enjrolas/L3D-Hardware/16x16x16 cube/3D model/corner.SLDPRT

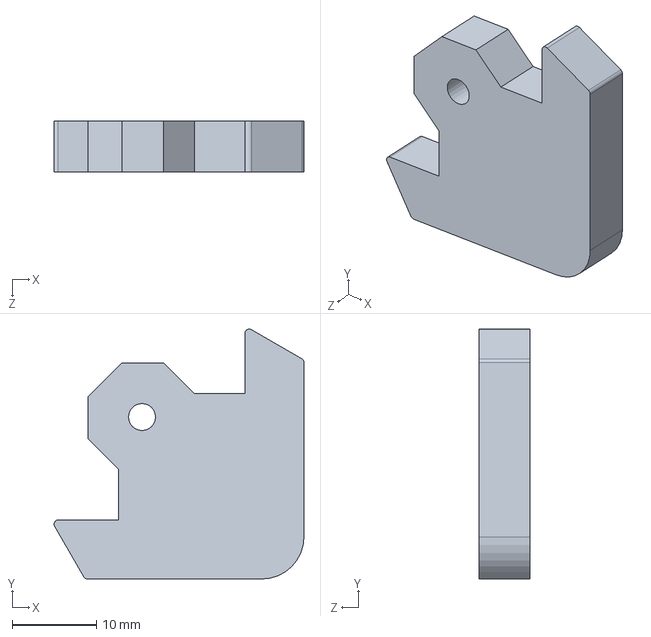
[picture p17: CAD file, 2017-03-31]
16x16x16 cube/3D model/corner.SLDPRT
29.6 x 29.6 x 6.00 mm
