enjrolas/L3D-Hardware/16x16x16 cube/3D model/pcb_strick.SLDPRT

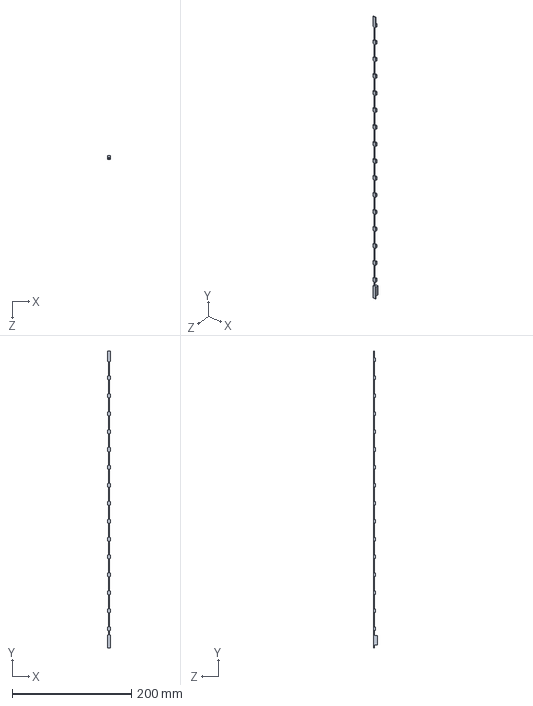
[picture p18: CAD file, 2017-03-31]
16x16x16 cube/3D model/pcb_strick.SLDPRT
5.58 x 497.5 x 6.00 mm
