enjrolas/L3D-Hardware/16x16x16 cube/3D model/white connector.SLDPRT

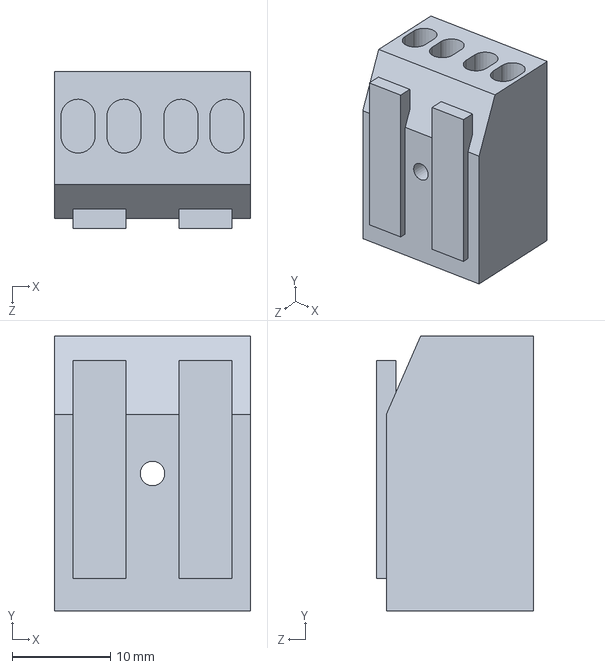
[picture p19: CAD file, 2017-03-31]
16x16x16 cube/3D model/white connector.SLDPRT
20.0 x 28.0 x 16.0 mm
