enjrolas/L3D-Hardware/16x16x16 cube/3D model/box_side1.SLDPRT

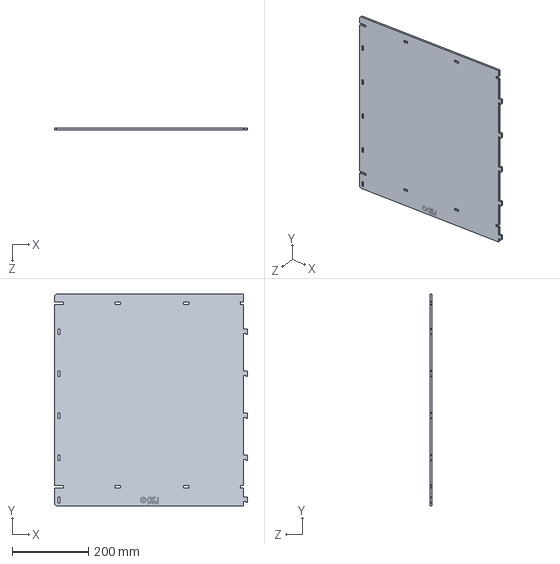
[picture p20: CAD file, 2017-03-31]
16x16x16 cube/3D model/box_side1.SLDPRT
505.4 x 555.0 x 6.00 mm
