enjrolas/L3D-Hardware/16x16x16 cube/3D model/face.SLDPRT

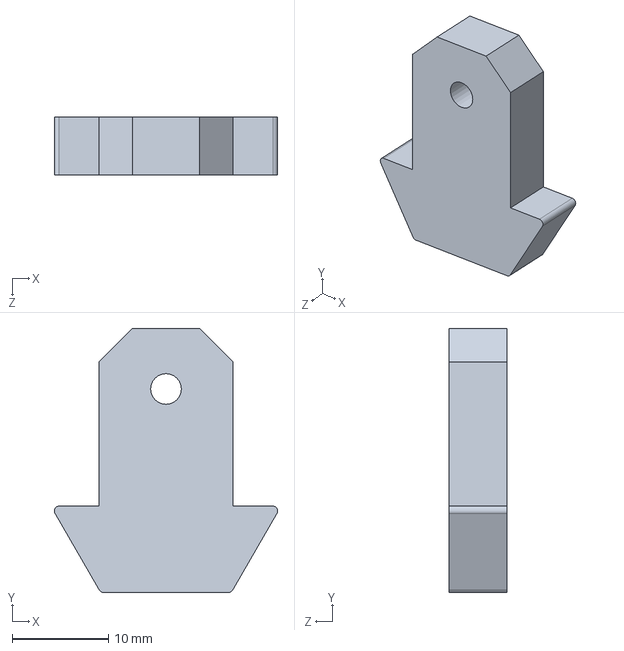
[picture p21: CAD file, 2017-03-31]
16x16x16 cube/3D model/face.SLDPRT
23.3 x 27.5 x 6.00 mm
